JDPennockGB/ENGR357-SDR-PennockRoque/Images/3D PCB Viewer.png

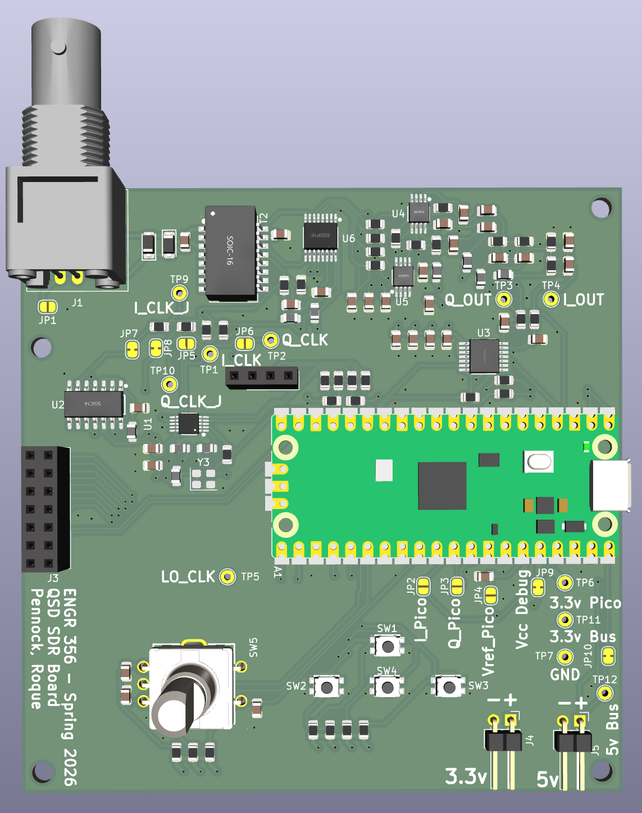
Images/3D PCB Viewer.png
