JDPennockGB/ENGR357-SDR-PennockRoque/Images/AudacityEnum.png

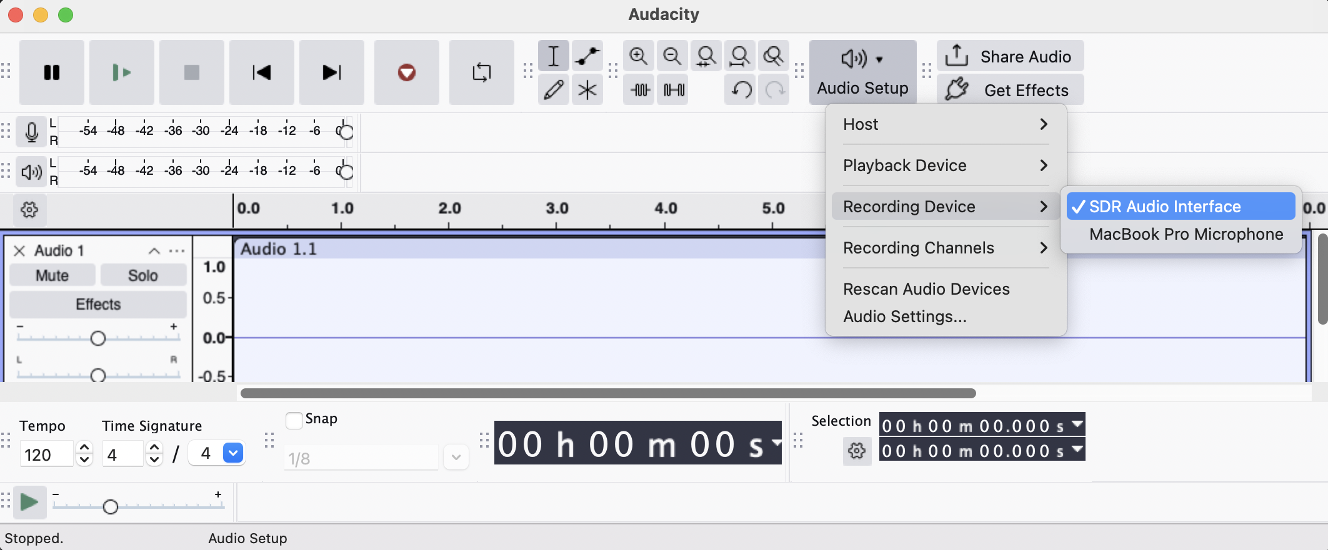
Images/AudacityEnum.png
