JDPennockGB/ENGR357-SDR-PennockRoque/Images/EncoderButtonsCircuit.png

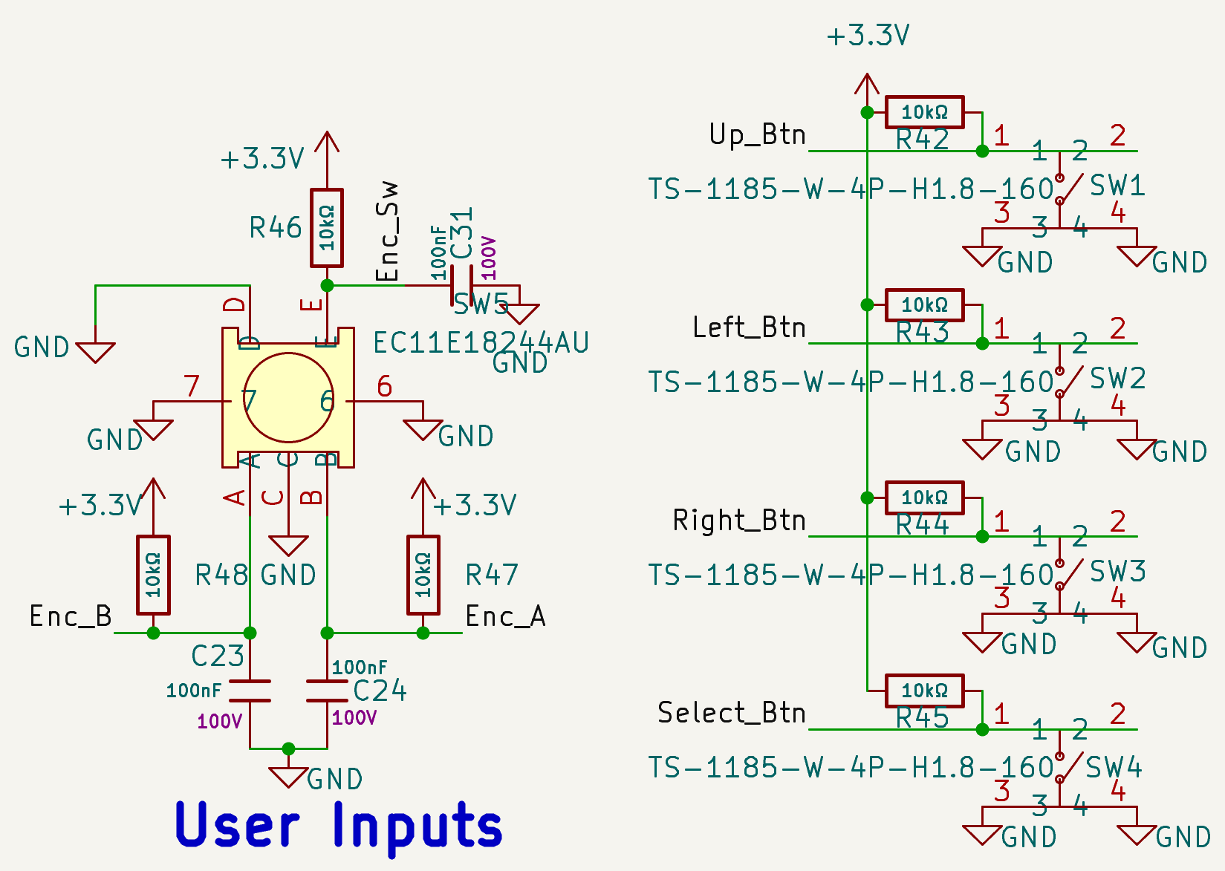
Images/EncoderButtonsCircuit.png
