JDPennockGB/ENGR357-SDR-PennockRoque/Images/I2CbusCircuit.png

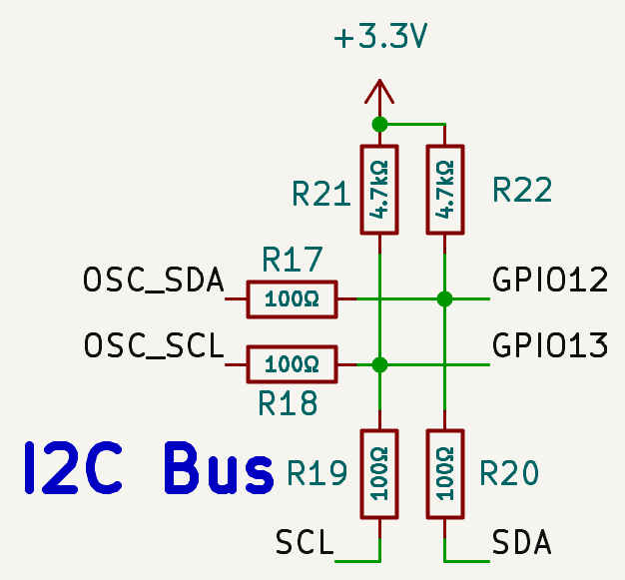
Images/I2CbusCircuit.png
