JDPennockGB/ENGR357-SDR-PennockRoque/Images/JohnsonClocks.JPG

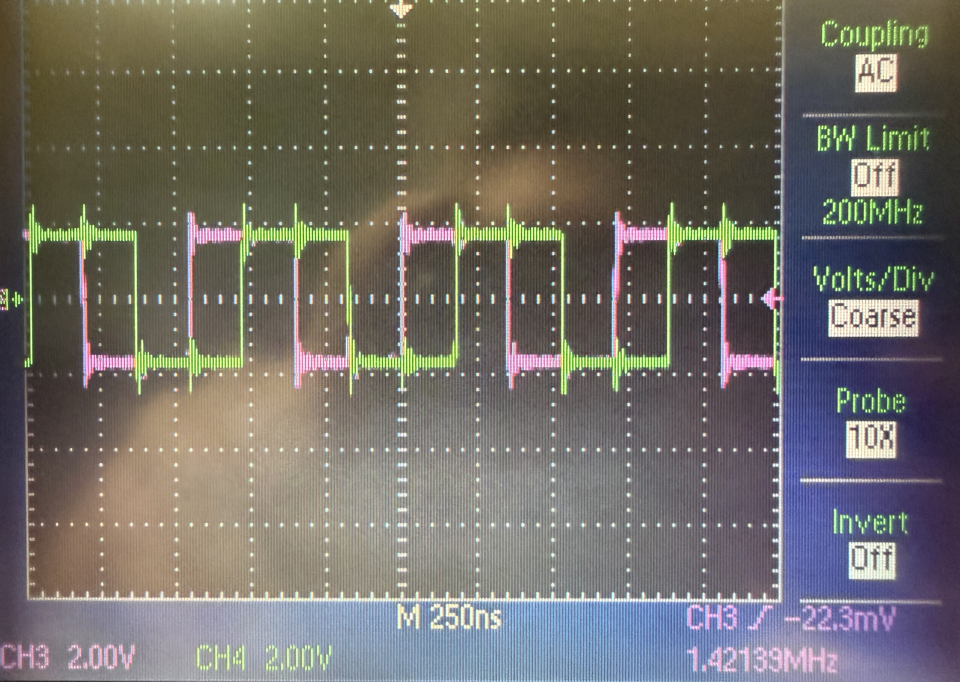
Images/JohnsonClocks.JPG
