JDPennockGB/ENGR357-SDR-PennockRoque/Images/LCDOLEDcircuit.png

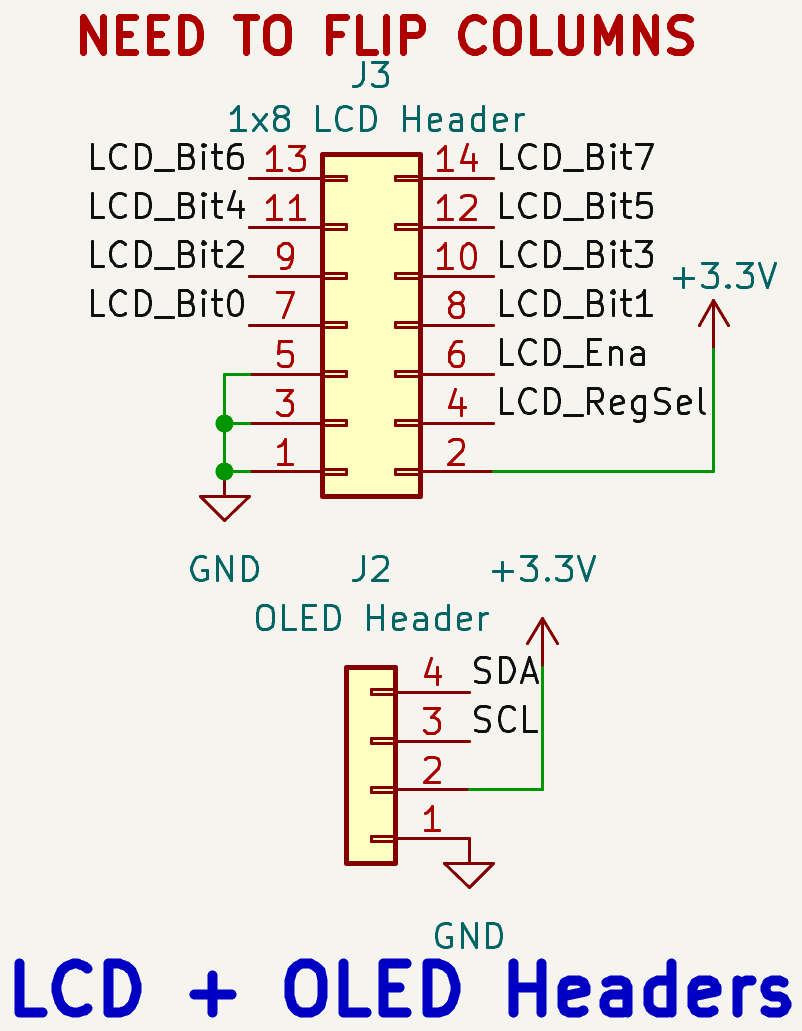
Images/LCDOLEDcircuit.png
