JDPennockGB/ENGR357-SDR-PennockRoque/Images/SDRinit.jpg

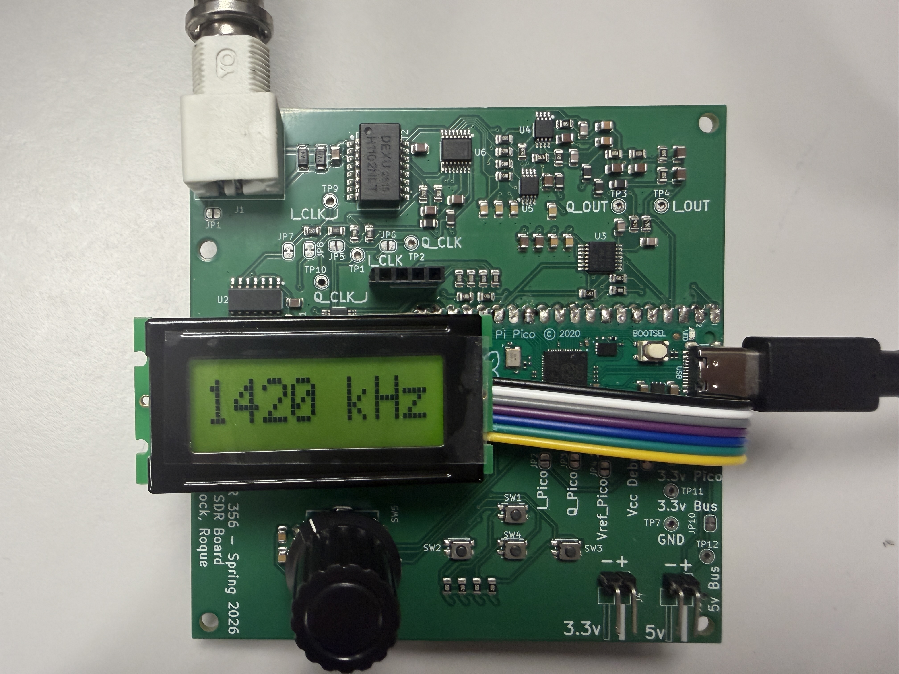
Images/SDRinit.jpg
