JDPennockGB/ENGR357-SDR-PennockRoque/Images/SDRmax.JPG

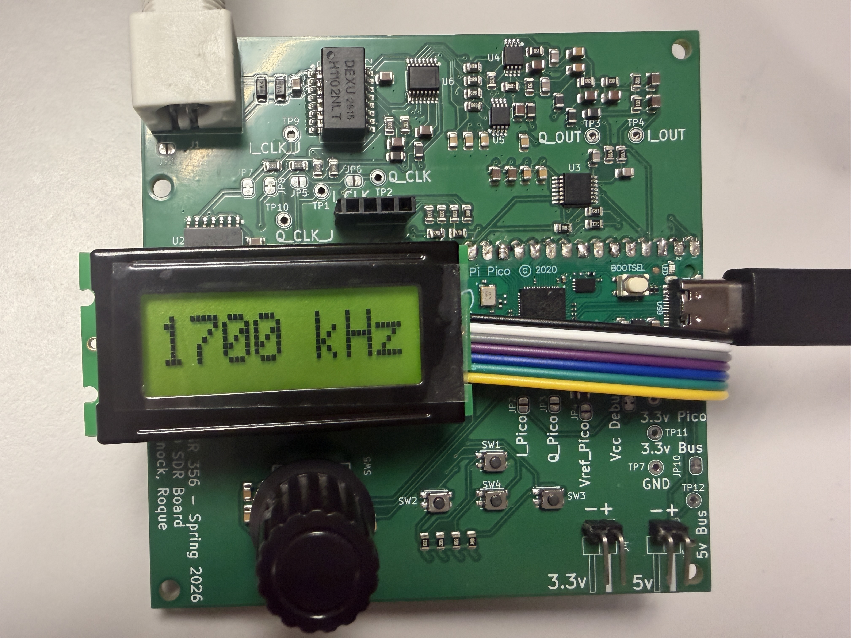
Images/SDRmax.JPG
