JDPennockGB/ENGR357-SDR-PennockRoque/Images/SDRmin.JPG

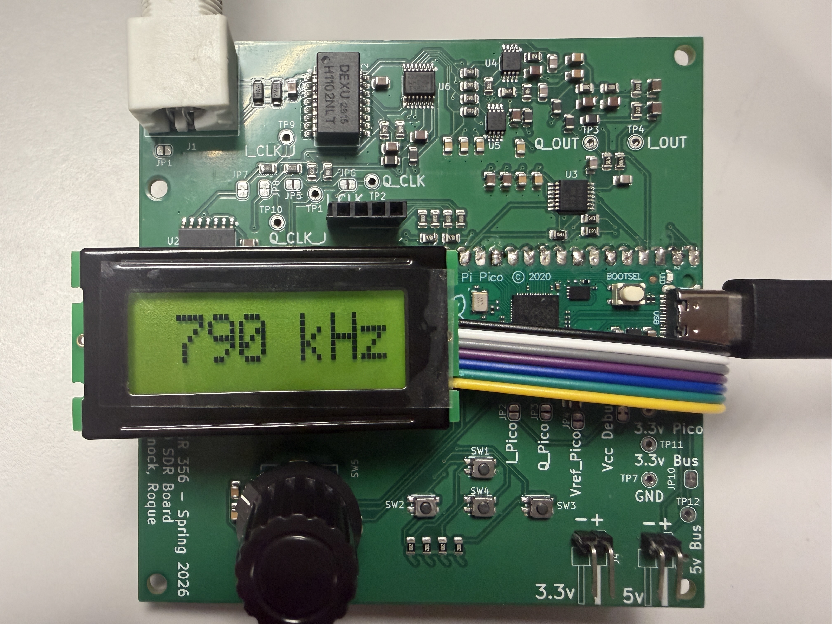
Images/SDRmin.JPG
