JDPennockGB/ENGR357-SDR-PennockRoque/Images/si5351Clock.JPG

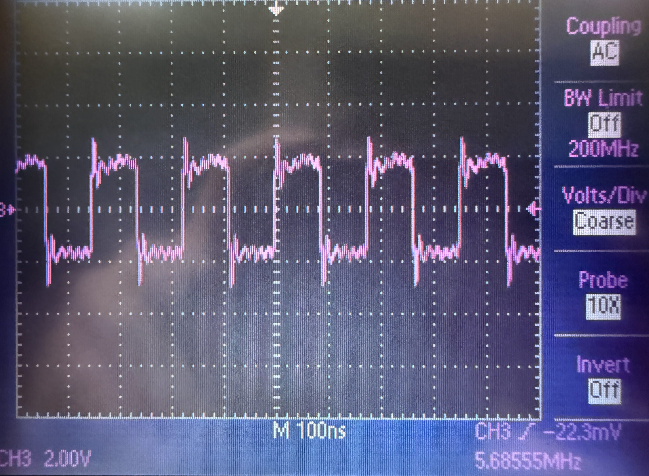
Images/si5351Clock.JPG
