JDPennockGB/ENGR357-SDR-PennockRoque/Images/TayloeDetectorCircuit.png

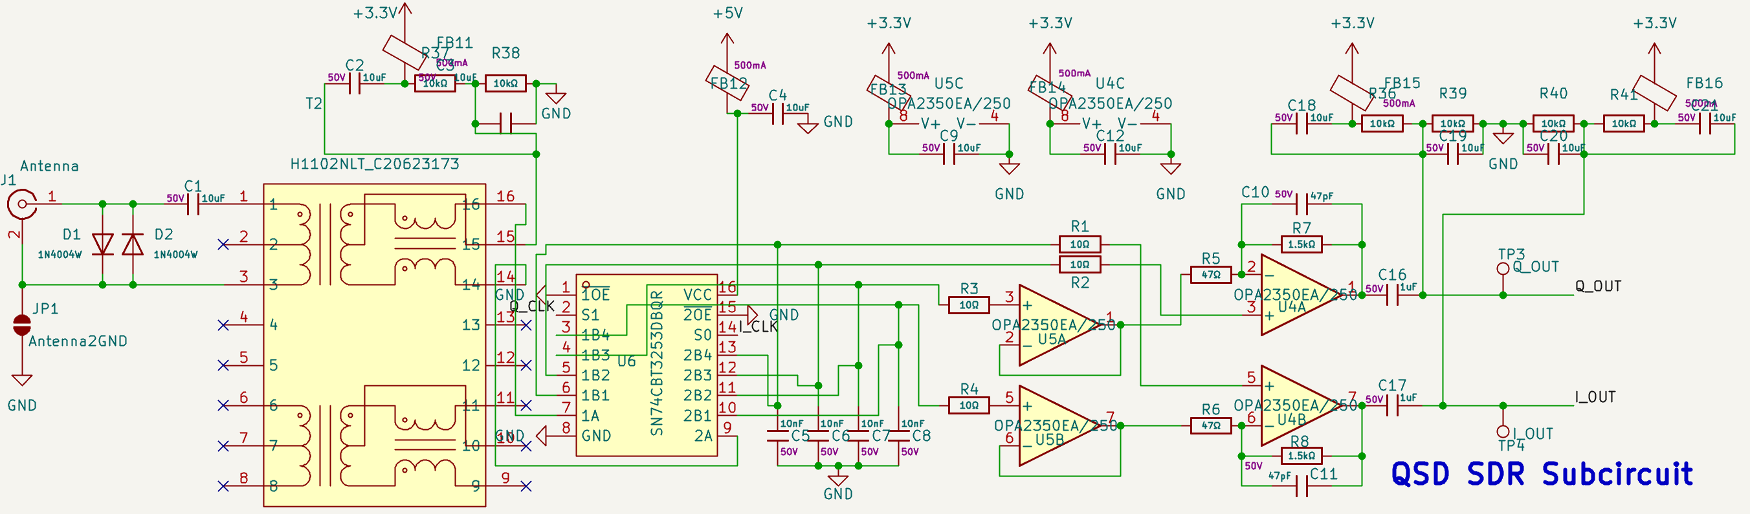
Images/TayloeDetectorCircuit.png
