JDPennockGB/ENGR357-SDR-PennockRoque/Images/UAC1Enum.png

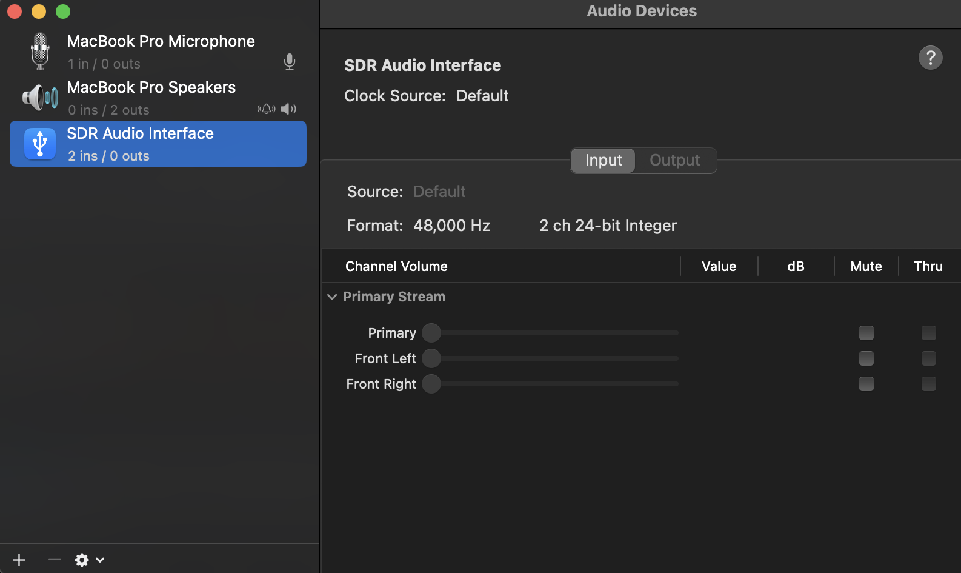
Images/UAC1Enum.png
