JDPennockGB/ENGR357-SDR-PennockRoque/Milestones-Documentation/Milestone4-CircuitNoiseSimulations/Simulation Results/ERRORMixerAmpSimImage.png

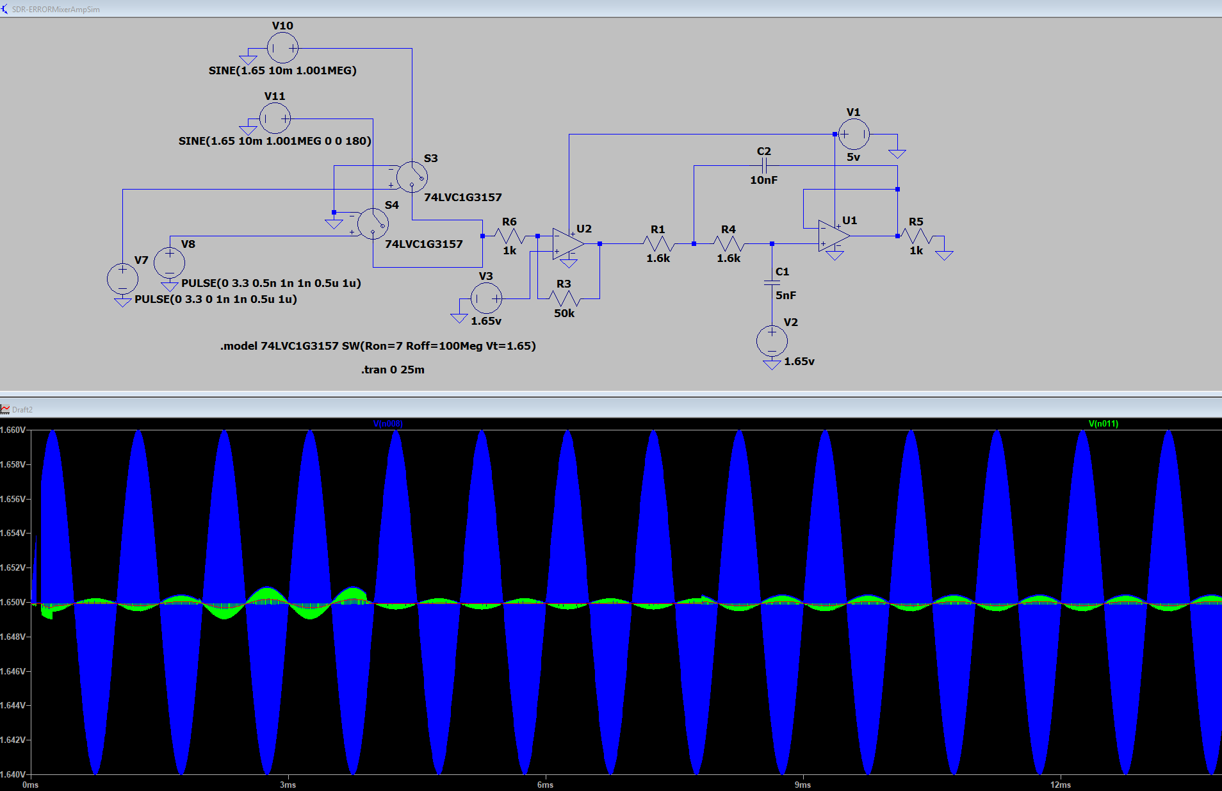
Milestones-Documentation/Milestone4-CircuitNoiseSimulations/Simulation Results/ERRORMixerAmpSimImage.png
