JDPennockGB/ENGR357-SDR-PennockRoque/Milestones-Documentation/Milestone4-CircuitNoiseSimulations/SDR-TayloeDetector-AmpStage.asc

C1: cap; 100µ
C2: cap; 100µ
C3: cap; 1µ
C4: cap; 1µ
R1: res; 10
R2: res; 10
R3: res; 10
R4: res; 10
R5: res; 470
R6: res; 470
R7: res; 10k
R8: res; 10k
U1: opamp
U2: opamp
U3: opamp
U5: opamp
