JDPennockGB/ENGR357-SDR-PennockRoque/Milestones-Documentation/Milestone4-CircuitNoiseSimulations/SDR-ERRORMixerAmpSim.asc

C1: cap; 5nF
C2: cap; 10nF
R1: res; 1.6k
R2: res; 1k
R3: res; 50k
R4: res; 1.6k
R5: res; 1k
R6: res; 1k
S3: sw; 74LVC1G3157
S4: sw; 74LVC1G3157
U1: UniversalOpAmp2
U2: UniversalOpAmp2
V1: voltage; 5v
V2: voltage; 1.65v
V3: voltage; 1.65v
V6: voltage; 1.4v
V7: voltage; PULSE(0 3.3 0 1n 1n 0.5u 1u)
V8: voltage; PULSE(0 3.3 0.5n 1n 1n 0.5u 1u)
V10: voltage; SINE(1.65 10m 1.001MEG)
V11: voltage; SINE(1.65 10m 1.001MEG 0 0 180)
Named nets: 0
.model 74LVC1G3157 SW(Ron=7 Roff=100Meg Vt=1.65)
Switch Mixer - Verified
Reference Voltage for Graph
.tran 0 25m
