JDPennockGB/ENGR357-SDR-PennockRoque/Milestones-Documentation/Milestone4-CircuitNoiseSimulations/SDR-SingalBoostAmpSim.asc

R1: res; 1K
R2: res; 47K
R3: res; 10K; tol=1 pwr=0.1
TL074: UniversalOpAmp2
V1: voltage; SINE(1.65 10mV 1kHz); AC 10mV
V2: voltage; 1.65v
V3: voltage; 3.3v
Named nets: 0
.tran 0 5m 0 1u
Singal Boost Amp Simulation - Verified
